uidaho/smartsettia-unit/script/my_globals.py

# This file contains the global variables used in smartsettia
import json
from time import sleep
import logging
version= "1.2.0"        # program version

# Note to concatonate dictionaries
# z = x.copy()
# z.update(y)

# Set domain being used
DOMAIN_INDEX = 0    # choose which domain. 0-2
DOMAIN =    ["https://smartsettia.com/",
            "https://smartsettia-backburn.c9users.io/",
            "https://smartsettia-nkrenowicz.c9users.io/"]

# set by arguments to disable GPIO
NOT_PI = False
FAKEWEBCAM = False

sensor_data = {}    # declare variable. Done as dictionary so that this can be imported with dic.update()            
sensor_data["sensor_data"] = [
            { "name": "cpu",         "type": "cpu_temperature", "value": "0.00" },  # pi system temperature
            { "name": "light_in",    "type": "light",           "value": "0.00" },  # ambiant light sensor inside
            { "name": "light_out",   "type": "light",           "value": "0.00" },  # ambiant light sensor outside
            { "name": "temperature", "type": "temperature",     "value": "0.00" },
            { "name": "humidity",    "type": "humidity",        "value": "0.00" }
#           { "name": "moisture_01", "type": "moisture",        "value": "0.00" },
#           { "name": "moisture_02", "type": "moisture",        "value": "0.00" }
            ]

# possible cover_statuses
# cover_status = { open, close, opening, closing, locked, error }

# possible server commands
# server_command = { open, close, lock }
status =        {"cover_status"   : "error",
                "server_command"  : None,
                "server_override" : False,      # will allow the sending of server_command back to server which will override server's state
                "error_msg"       : None
                }

settings =      {"Config_Version": 5,    ### INCREMENT THIS IF SETTING STRUCTURE CHANGED ###
                "name":"UnNamed",                          # Name of Device
                "uuid": "NOT_SET0-0000-0000-0000-000000000000",   # UUID V1
                "token": "none",      # post token key
                "id": -1,                                   # ID no. of the device
                "challenge": "TacosToTheLimit2017",                    # challenge
                "mac_address":"00:00:00:00:00:00",          # MAC address
                "server_reg_addr":    DOMAIN[DOMAIN_INDEX] + "api/register",
                "server_status_addr": DOMAIN[DOMAIN_INDEX] + "api/update",
                "server_sensor_addr": DOMAIN[DOMAIN_INDEX] + "api/sensor",
                "server_img_addr":    DOMAIN[DOMAIN_INDEX] + "api/image",
                "job_cover_monitor":2,                      # cover monitor run rate
                "job_save_settings":60,                     # save settings to file
                "job_webcam_sec"   :15,                      # job runs every x seconds
                "job_server_status_sec" :2,                 # send device status job
                "job_server_sensors_sec":60,                # send device sensors job
                                                            # other jobs
                "cover_time_open":  None,                   # open time
                "cover_time_close": None,                   # close time
                "schedule_last_checked": None,              # last time we checked the schedual
                "storage_dir": "/mnt/ramdisk/",             # directory where picture & logs are saved do
                "img_name": "webcam_img.jpg",               # name of webcam picture
                "config_dir": "/var/log/smartsettia/config.json"  # dir and filename for config file
                }


def save_settings():
    logging.info("Saving settings")
    global settings
    #print ("Settings dump: ",settings)         # debugger
    try:
        with open(settings['config_dir'], 'w') as f:
            json.dump(settings, f)
    except Exception as e:
        logging.error ("Save settings error %r" % e)


def load_settings():
    logging.info ("Loading settings")
    global settings
    temp = {}
    try:
        with open(settings['config_dir'], 'r') as f:
            temp = json.load(f)
    # except FileNotFoundError:
    #    print "config.json file not found. loading default settings"
    except Exception as e:
        logging.warning ("\tLoad settings error %r"% e)
        sleep(3)

    else:       # if file was found and all is good
        # print temp             # debugger
        # test if loaded config version matches default version number
        try: 
            if temp["Config_Version"] != settings["Config_Version"]:
                logging.warning ("\tConfig Version does not match.")
                logging.info ("\tUsing default settings")
                sleep(3)
                return
        except:
                logging.warning ("\tConfig Version error.")   # likely means its a really old config without config_version entry
                logging.info ("\tUsing default settings")
                sleep(3)
                return
        
        # Test if uuid's are matching.
        if temp["uuid"] == settings["uuid"]:
            logging.info ("\tUUID matches loaded settings - keeping")
            settings = temp     # set settings to loaded values

            # override loaded url's to match DOMAIN_INDEX
            update_url(DOMAIN[DOMAIN_INDEX])

        else:
            logging.warning ("\tUUID does not mach loaded settings - discarding")
            logging.info ("\tUsing default settings")
            sleep(3)

def update_url(domain):
    global settings
    
    # ending '/' test. Add if missing
    mlen = len(domain) - 1
    if (domain[mlen] != '/'):
        domain = domain + '/'
    
    logging.info ("Using domain %s" % domain)
    settings["server_reg_addr"]    = domain + "api/register"
    settings["server_status_addr"] = domain + "api/update"
    settings["server_sensor_addr"] = domain + "api/sensor"
    settings["server_img_addr"]    = domain + "api/image"
    logging.debug ("\tURL register: %s" % settings["server_reg_addr"])
    logging.debug ("\tURL status:   %s" % settings["server_status_addr"])
    logging.debug ("\tURL sensors:  %s" % settings["server_sensor_addr"])
    logging.debug ("\tURL image:    %s" % settings["server_img_addr"])
